romadanylchuk/acoustic-system/hardware/schematics/station/station.kicad_sch

## KiCad design hardware/schematics/station/station.kicad_sch (2026-04-08)

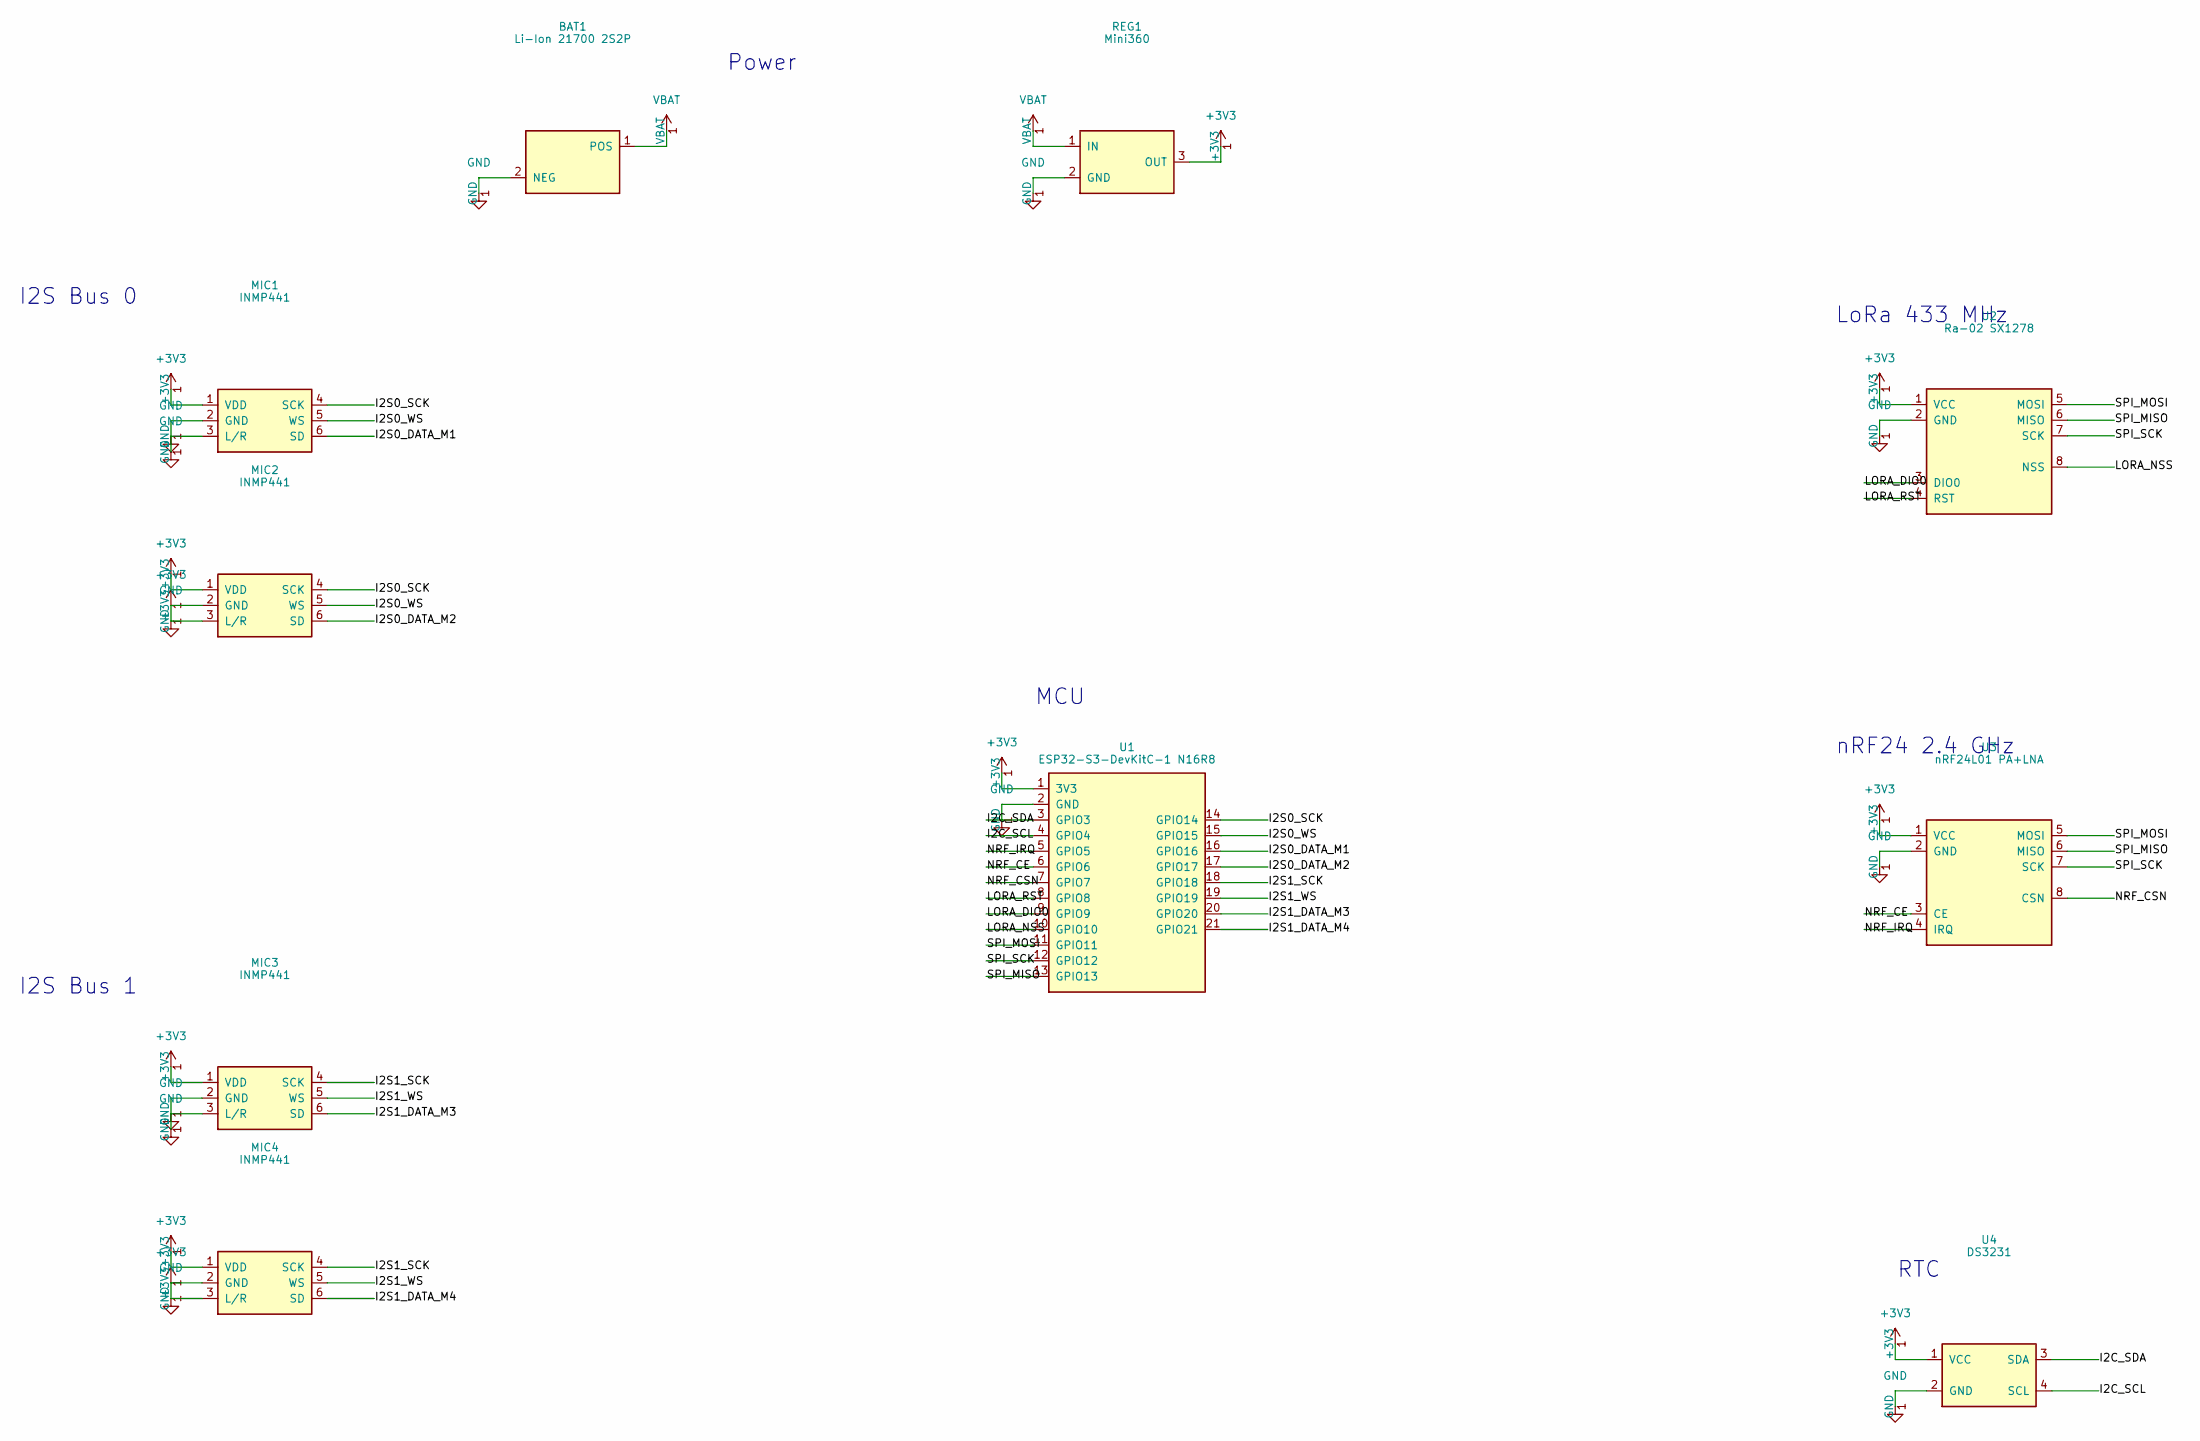
[picture p3: schematic station.kicad_sch]

Parts:
BAT1: Li-Ion 21700 2S2P
MIC1, MIC2, MIC3, MIC4: INMP441
REG1: Mini360
U1: ESP32-S3-DevKitC-1 N16R8
U2: Ra-02 SX1278
U3: nRF24L01 PA+LNA
U4: DS3231

Connections:
+3V3: BAT1.2 (NEG), MIC1.1 (VDD), MIC1.2 (GND), MIC1.3 (L/R), MIC2.1 (VDD), MIC2.2 (GND), MIC2.3 (L/R), MIC3.1 (VDD), MIC3.2 (GND), MIC3.3 (L/R), MIC4.1 (VDD), MIC4.2 (GND), MIC4.3 (L/R), REG1.2 (GND), REG1.3 (OUT), U1.1 (3V3), U1.2 (GND), U1.3 (GPIO3), U2.1 (VCC), U2.2 (GND), U3.1 (VCC), U3.2 (GND), U4.1 (VCC), U4.2 (GND), U4.3 (SDA)
I2C_SCL: U1.4 (GPIO4), U4.4 (SCL)
I2S0_DATA_M1: MIC1.6 (SD), U1.16 (GPIO16)
I2S0_DATA_M2: MIC2.6 (SD), U1.17 (GPIO17)
I2S0_SCK: MIC1.4 (SCK), MIC2.4 (SCK), U1.14 (GPIO14)
I2S0_WS: MIC1.5 (WS), MIC2.5 (WS), U1.15 (GPIO15)
I2S1_DATA_M3: MIC3.6 (SD), U1.20 (GPIO20)
I2S1_DATA_M4: MIC4.6 (SD), U1.21 (GPIO21)
I2S1_SCK: MIC3.4 (SCK), MIC4.4 (SCK), U1.18 (GPIO18)
I2S1_WS: MIC3.5 (WS), MIC4.5 (WS), U1.19 (GPIO19)
LORA_DIO0: U1.9 (GPIO9), U2.3 (DIO0)
LORA_NSS: U1.10 (GPIO10), U2.8 (NSS)
LORA_RST: U1.8 (GPIO8), U2.4 (RST)
NRF_CE: U1.6 (GPIO6), U3.3 (CE)
NRF_CSN: U1.7 (GPIO7), U3.8 (CSN)
NRF_IRQ: U1.5 (GPIO5), U3.4 (IRQ)
SPI_MISO: U1.13 (GPIO13), U2.6 (MISO), U3.6 (MISO)
SPI_MOSI: U1.11 (GPIO11), U2.5 (MOSI), U3.5 (MOSI)
SPI_SCK: U1.12 (GPIO12), U2.7 (SCK), U3.7 (SCK)
VBAT: BAT1.1 (POS), REG1.1 (IN)

Notes on the sheet:
RTC
LoRa 433 MHz
nRF24 2.4 GHz
MCU
Power
I2S Bus 0
I2S Bus 1
